Tow96/Tecladitow40/Firmware/rev0/TEST/src/pins.h

#ifndef PINS_H_
  #define PINS_H_

  #define rowA 18
  #define rowB 17
  #define rowC 16
  #define rowD 15

  #define col1 14
  #define col2 13
  #define col3 12
  #define col4 11
  #define col5 10
  #define col6 9
  #define col7 8
  #define col8 7
  #define col9 6
  #define col10 5
  #define col11 4
  #define col12 3

  const byte rowPins[] = {rowA, rowB, rowC, rowD};
  const byte colPins[] = {col1, col2, col3, col4, col5, col6, col7, col8, col9, col10, col11, col12};

#endif
